mirage335/PatchRap/documentation/labels/_ref/OpenClipArt/1280913718.png

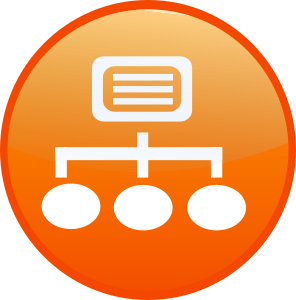
documentation/labels/_ref/OpenClipArt/1280913718.png
