mirage335/PatchRap/_out_PatchRap_symbols/_ref/diagrams/rambo/v1.0-v1.1_Rambo-conn-all.jpg

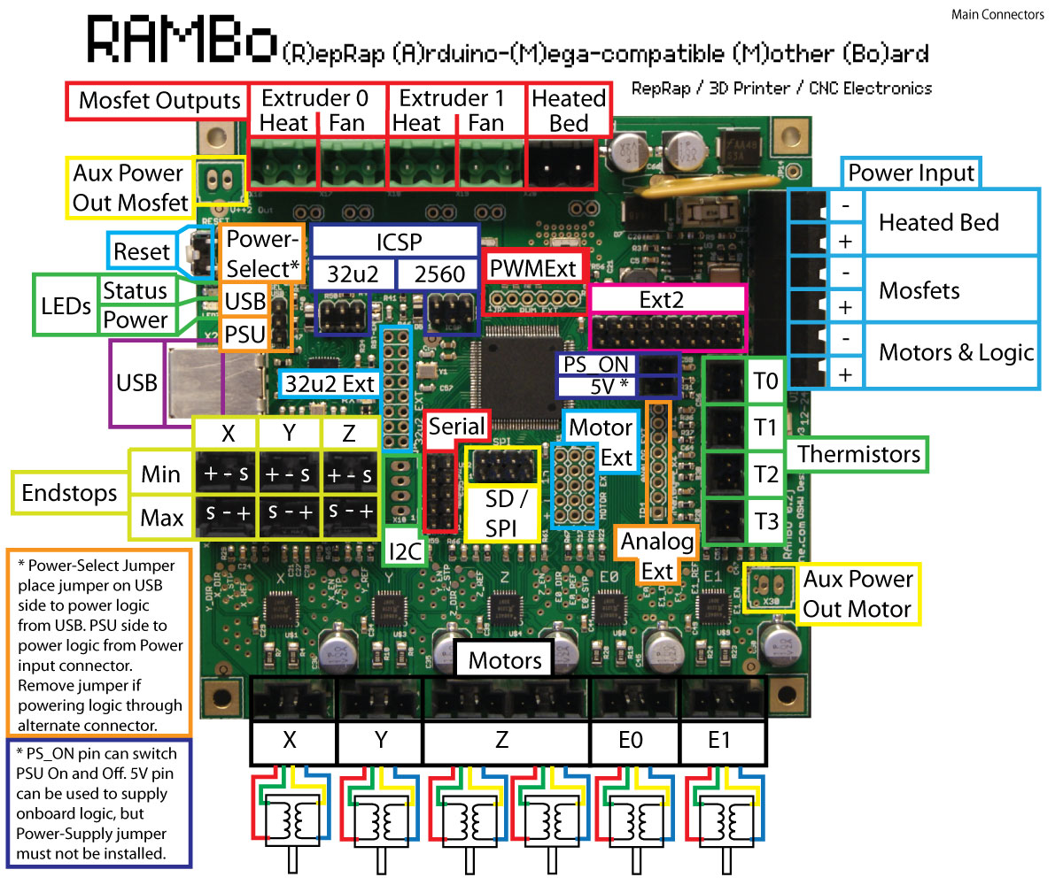
_out_PatchRap_symbols/_ref/diagrams/rambo/v1.0-v1.1_Rambo-conn-all.jpg
