mirage335/PatchRap/_out/_dev/PatchRap_FreeCAD/GenericRap/RenderBottom.png

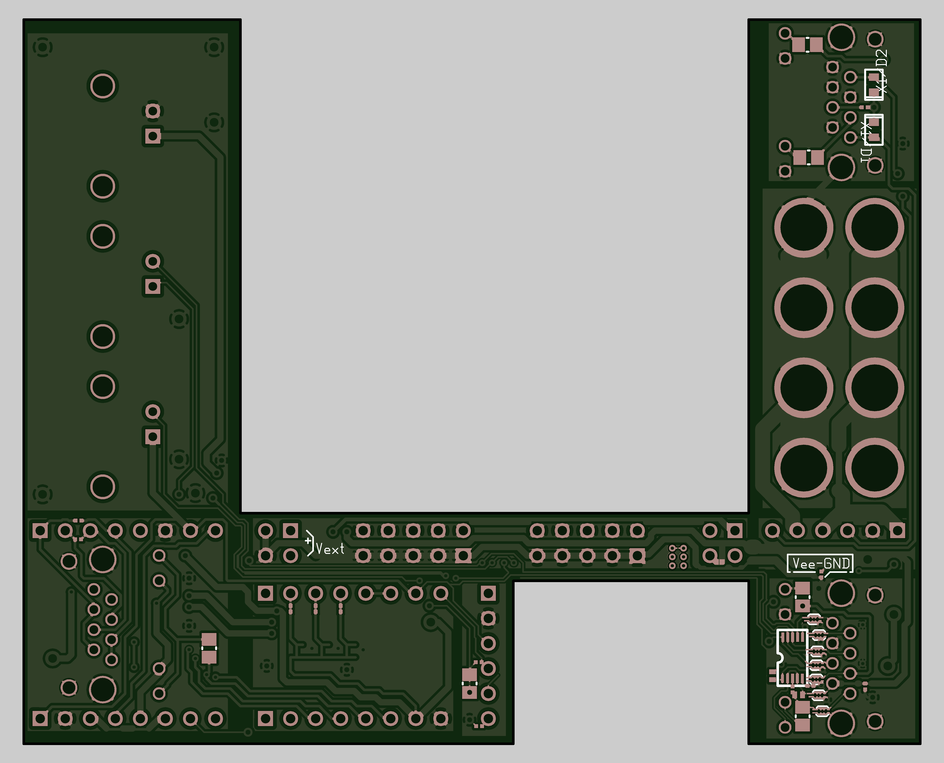
_out/_dev/PatchRap_FreeCAD/GenericRap/RenderBottom.png
