mirage335/PatchRap/_out/_dev/PatchRap_FreeCAD/GenericRap/RenderTop.png

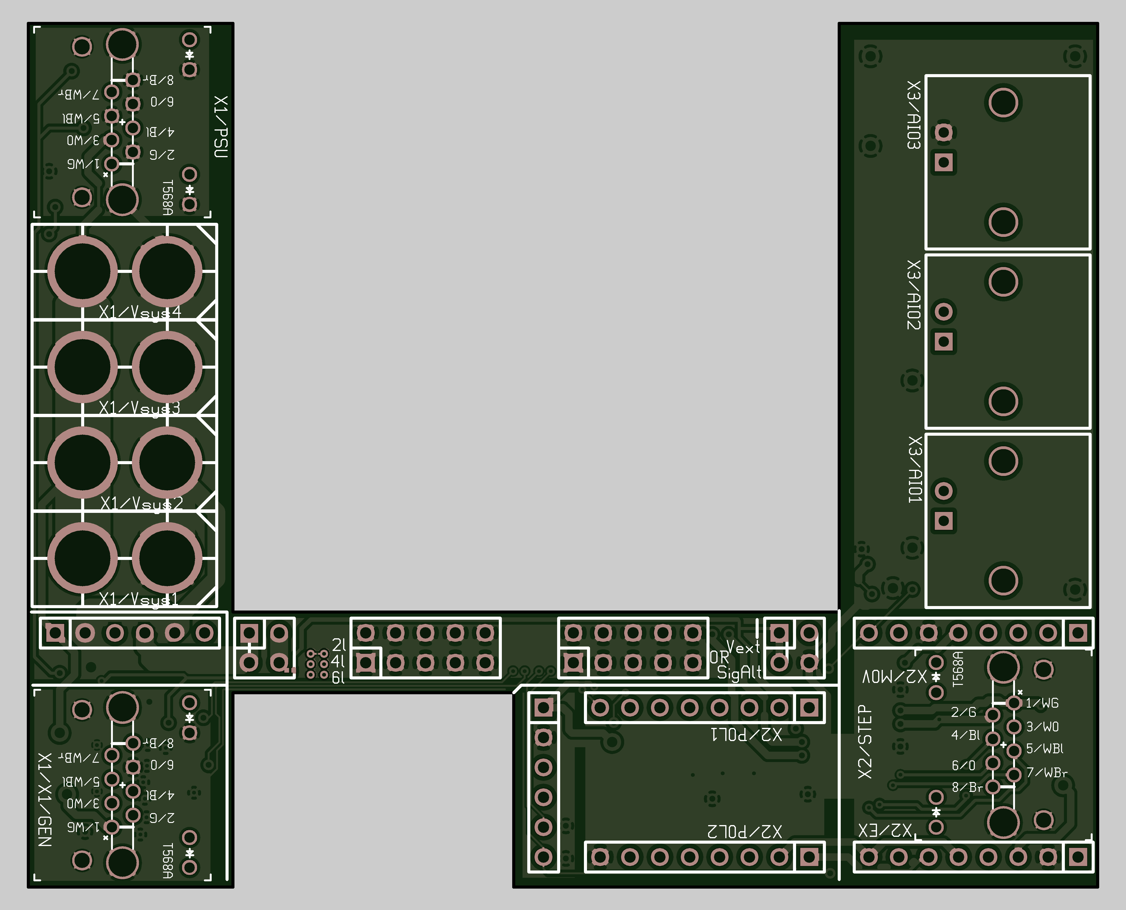
_out/_dev/PatchRap_FreeCAD/GenericRap/RenderTop.png
