mirage335/PatchRap/_out_PatchRap_symbols/_ref/diagrams/lulzbot/Taz Extruder Pin Assignments v2c.jpg

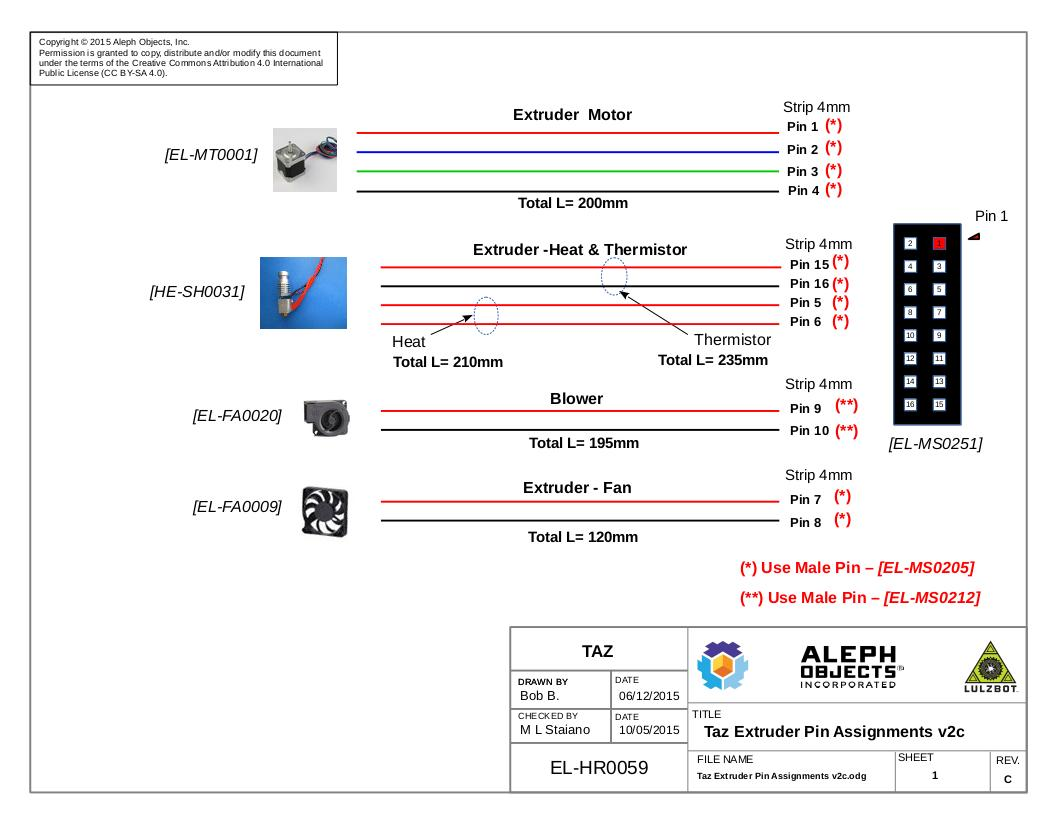
_out_PatchRap_symbols/_ref/diagrams/lulzbot/Taz Extruder Pin Assignments v2c.jpg
