mirage335/PatchRap/_out_PatchRap_symbols/_ref/diagrams/rambo/MiniRambo_v1.3.png

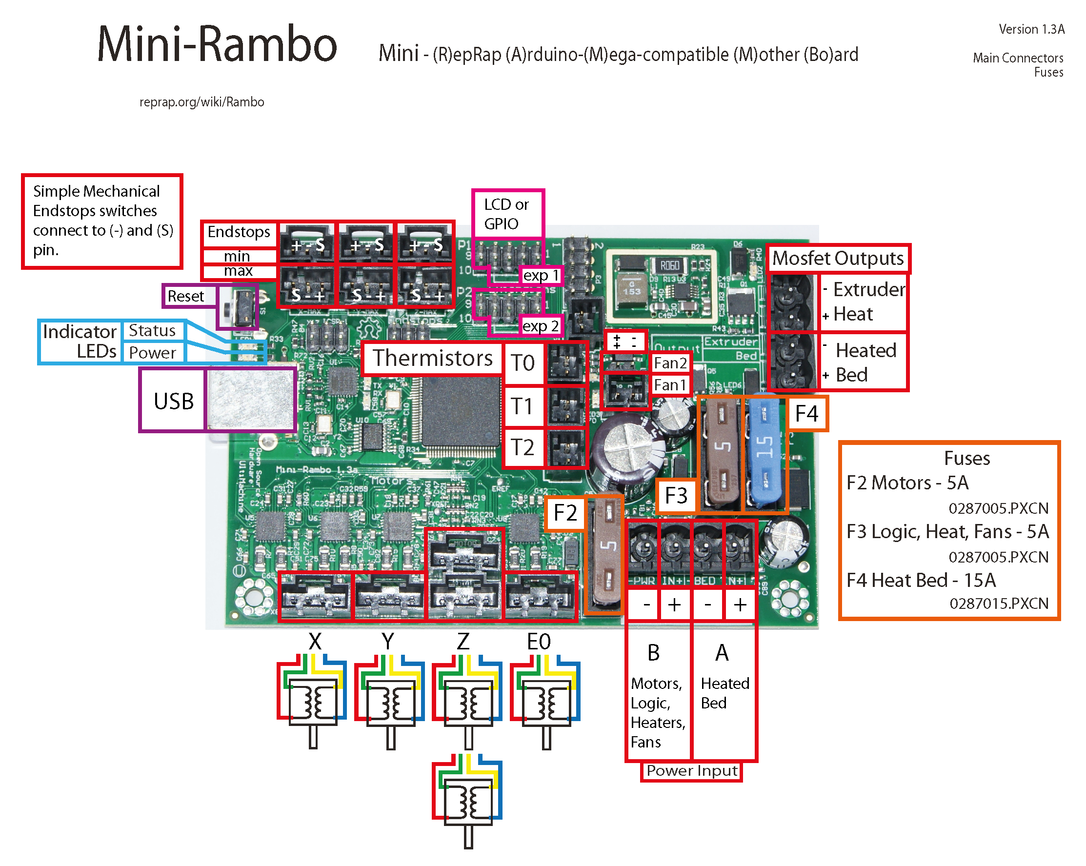
_out_PatchRap_symbols/_ref/diagrams/rambo/MiniRambo_v1.3.png
