mirage335/PatchRap/_out_PatchRap_symbols/_ref/diagrams/rambo/v1.4_Rambo-1.4-connection-diagram.png

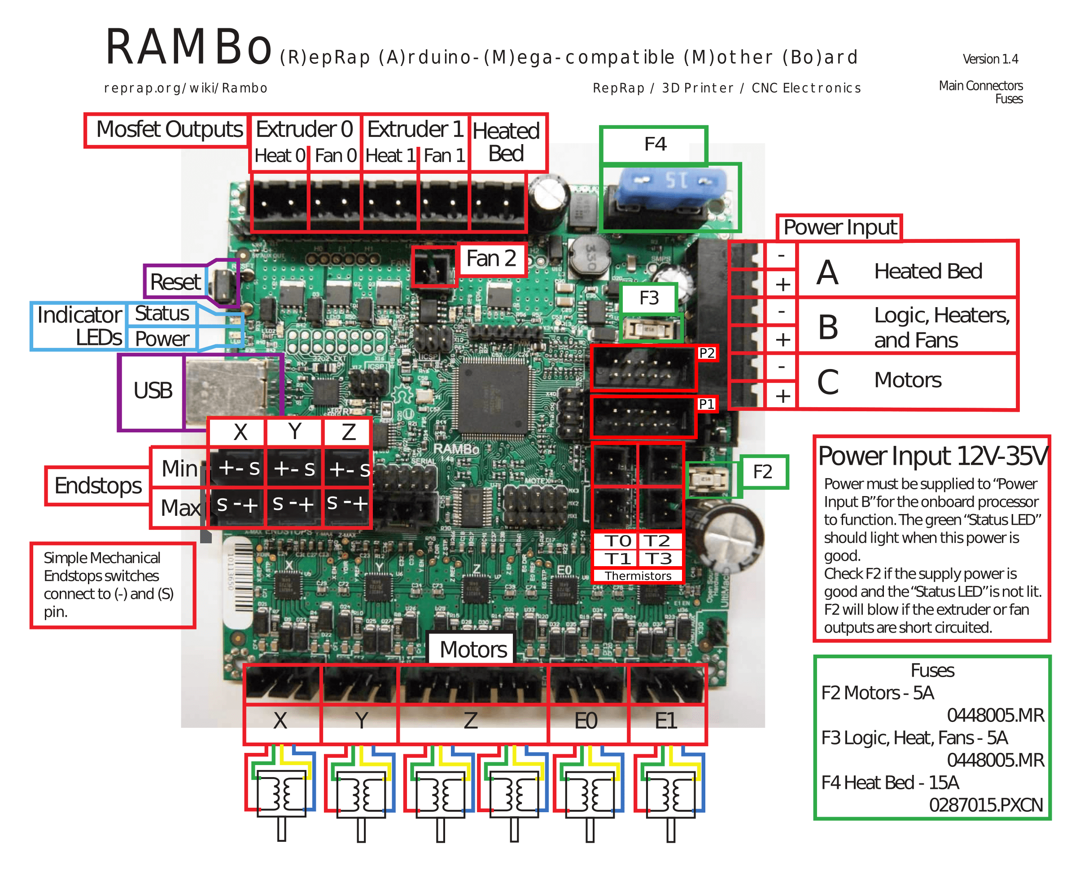
_out_PatchRap_symbols/_ref/diagrams/rambo/v1.4_Rambo-1.4-connection-diagram.png
