mirage335/PatchRap/_out_PatchRap_symbols/footprints/illustration_extruder_typical_RenderTop.png

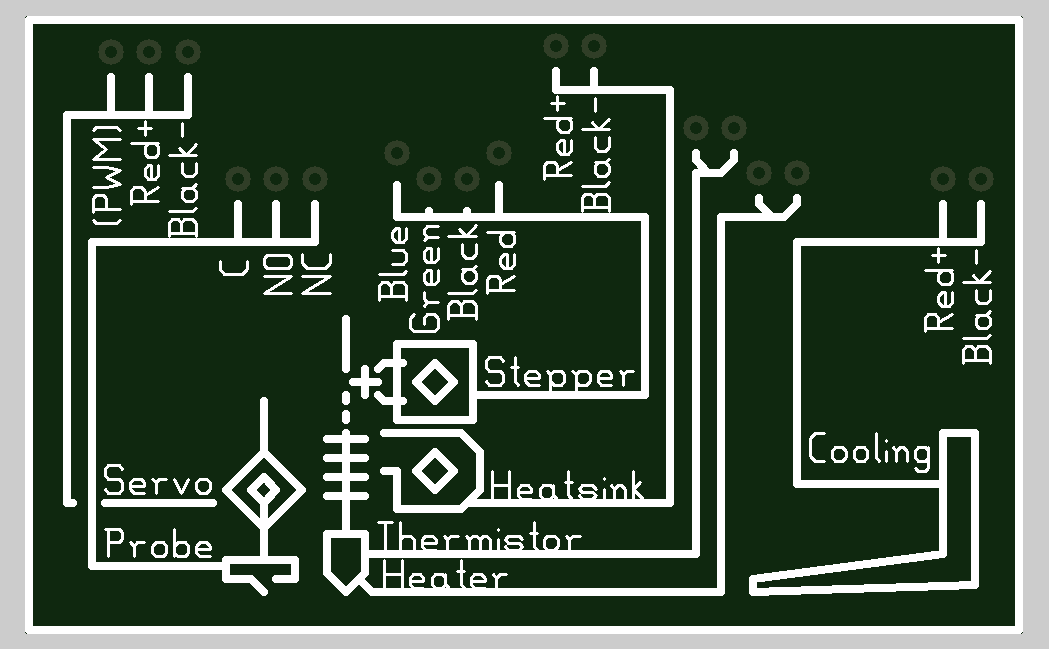
_out_PatchRap_symbols/footprints/illustration_extruder_typical_RenderTop.png
