mirage335/PatchRap/documentation/labels/_ref/OpenClipArt/earthquake.png

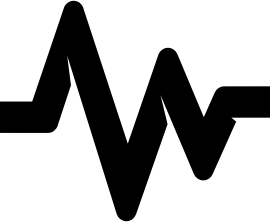
documentation/labels/_ref/OpenClipArt/earthquake.png
