mirage335/PatchRap/documentation/labels/_ref/OpenClipArt/RootTerminal.png

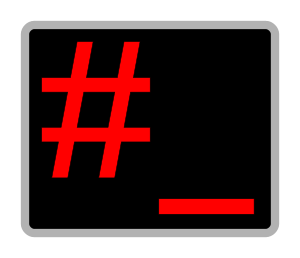
documentation/labels/_ref/OpenClipArt/RootTerminal.png
