mirage335/PatchRap/documentation/labels/_ref/OpenClipArt/warning-02.png

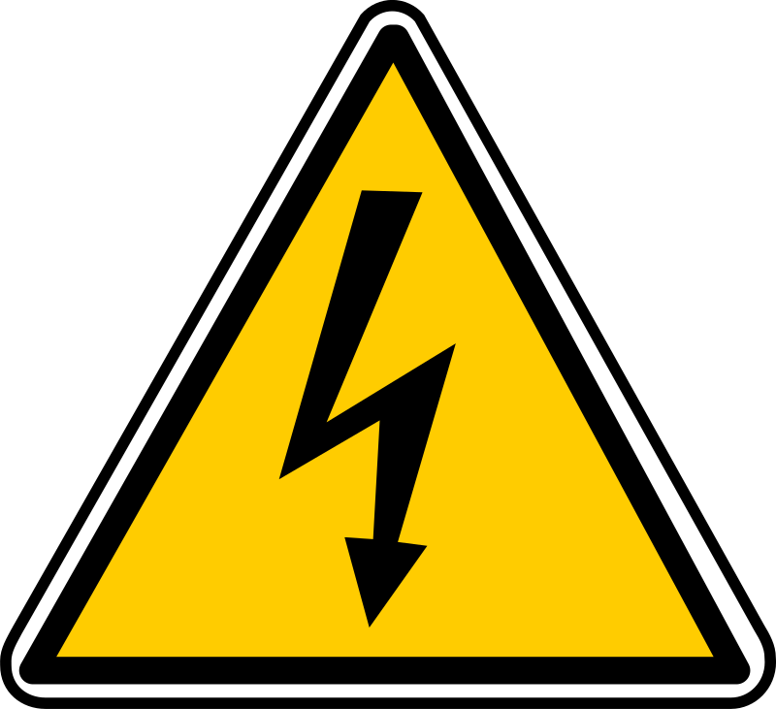
documentation/labels/_ref/OpenClipArt/warning-02.png
