mirage335/PatchRap/documentation/labels/labels/Analog.png

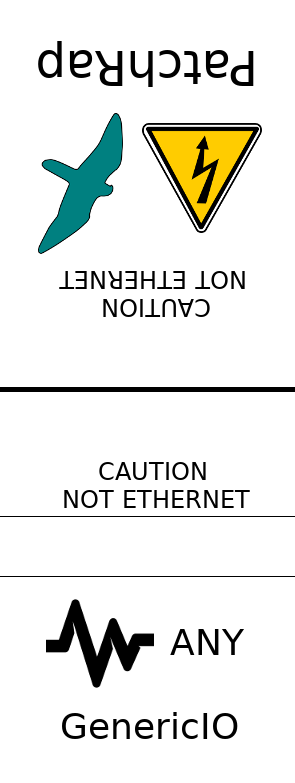
documentation/labels/labels/Analog.png
