mirage335/PatchRap/documentation/labels/labels/Core.png

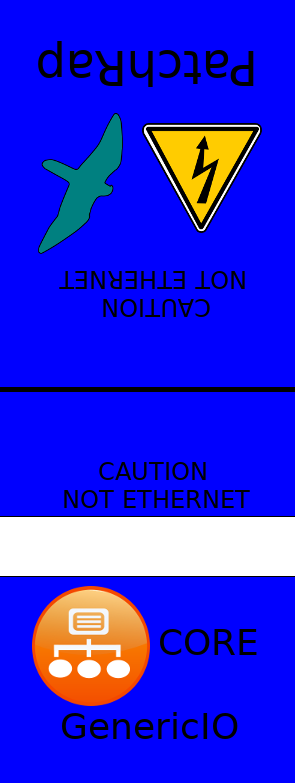
documentation/labels/labels/Core.png
