mirage335/PatchRap/documentation/labels/labels/Digital.png

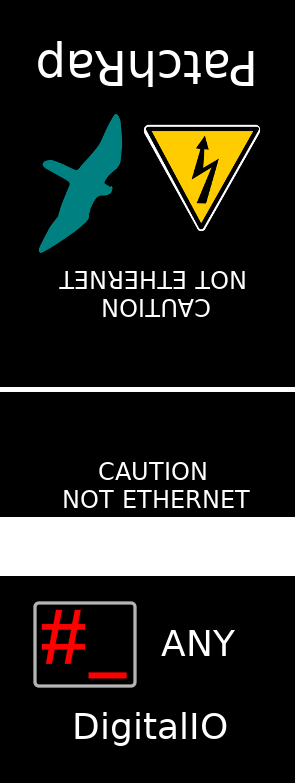
documentation/labels/labels/Digital.png
