mirage335/PatchRap/documentation/labels/labels/HotendT0.png

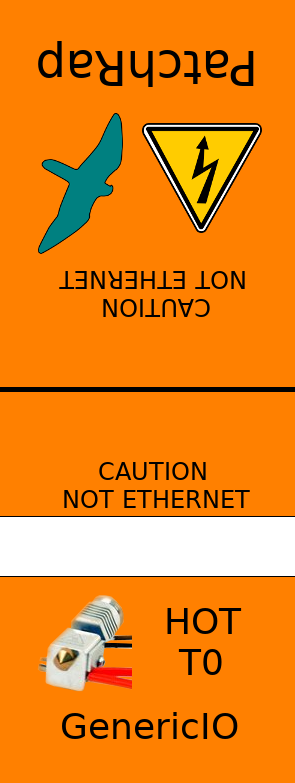
documentation/labels/labels/HotendT0.png
