mirage335/PatchRap/documentation/labels/labels/LimitX.png

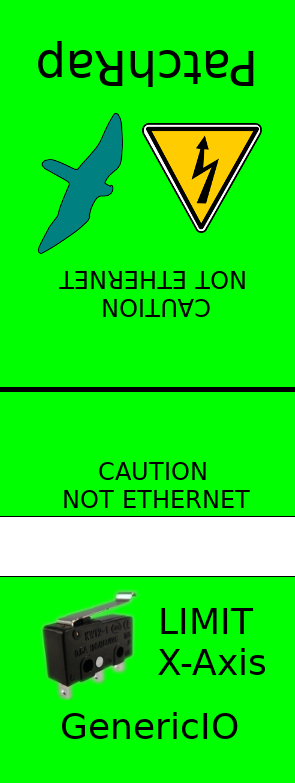
documentation/labels/labels/LimitX.png
