mirage335/PatchRap/documentation/labels/labels/MotorT0.png

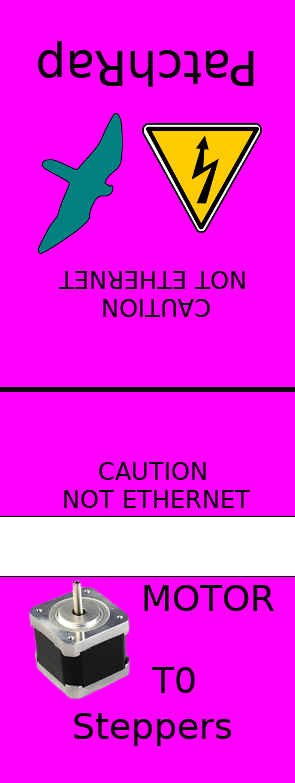
documentation/labels/labels/MotorT0.png
