mirage335/PatchRap/documentation/labels/labels/MotorYfwd.png

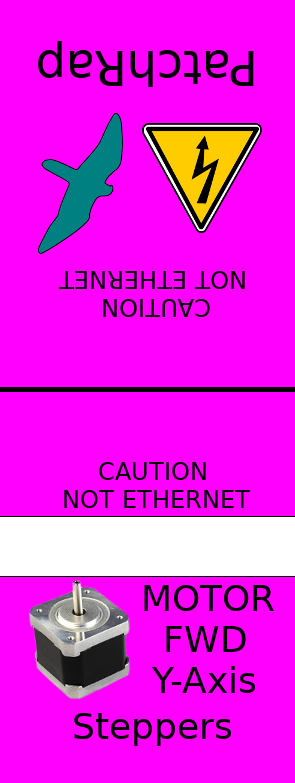
documentation/labels/labels/MotorYfwd.png
