mirage335/PatchRap/documentation/labels/panels/comprehensive.png

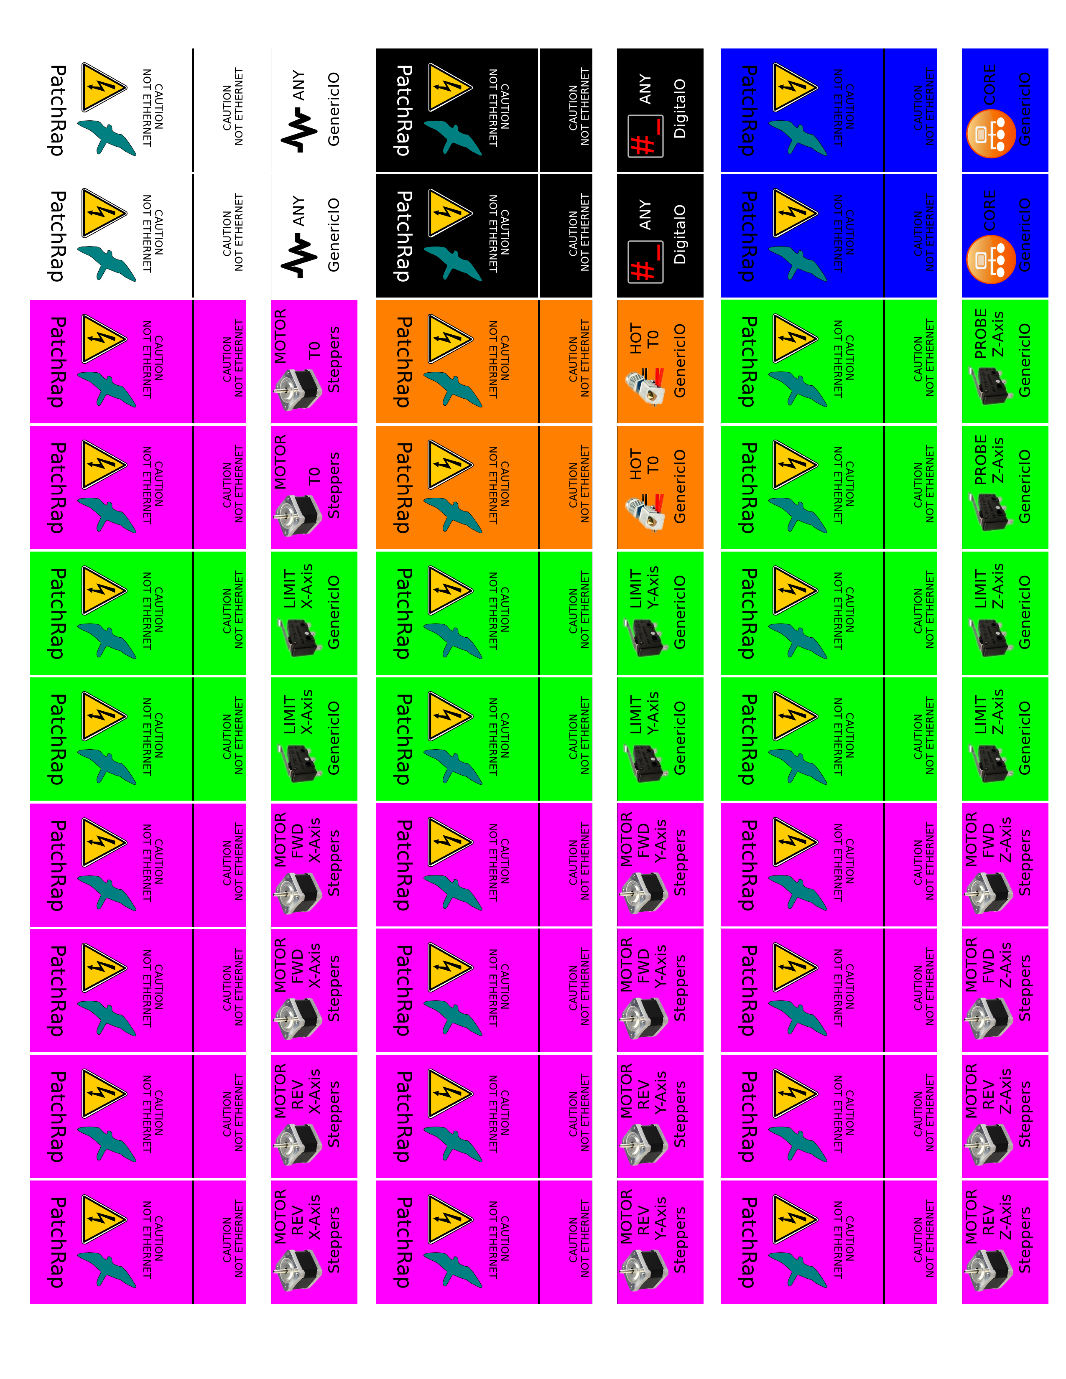
documentation/labels/panels/comprehensive.png
